lishen2/BBGun/firmware/source/button.h

#ifndef _BUTTON_H_
#define _BUTTON_H_

enum{
	BUTTON_NOKEY,
	BUTTON_FIRE,
	BUTTON_RELOAD,
	BUTTON_CANCEL,
	BUTTON_ENTER,
	BUTTON_UP,
	BUTTON_DOWN,
};

void button_init(void);
int button_get(void);

#endif
